pp3times/zmk-config-drift-v3-editor/PS3 Battery Pack Assembly/Drift-V3-Bottom-Pieces/Drift-V3-Bottom-Pieces.3mf

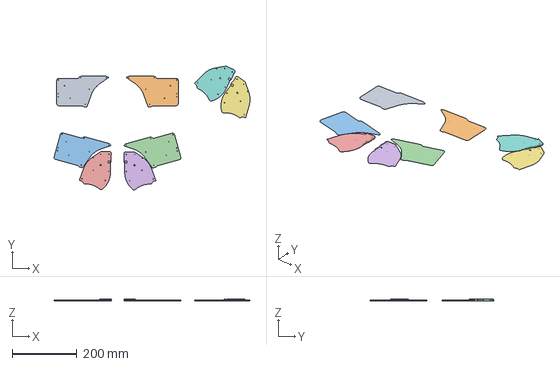
[picture p75: CAD file, 2025-06-20, last stored version]
PS3 Battery Pack Assembly/Drift-V3-Bottom-Pieces/Drift-V3-Bottom-Pieces.3mf
606.4 x 383.0 x 5.00 mm
Drift V3 bottom left.stl x 4
Drift V3 bottom right.stl x 4
