pp3times/zmk-config-drift-v3-editor/V3-MCU-Cover/MCU-Cover-left.stl

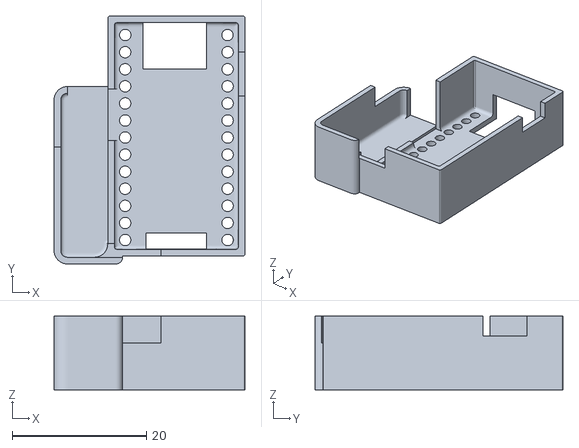
[picture p76: CAD file, 2025-06-20, last stored version]
V3-MCU-Cover/MCU-Cover-left.stl
28.4 x 36.9 x 11.0
