pp3times/zmk-config-drift-v3-editor/Outer-Acrylic/Bottom-Left-Acrylic.stl

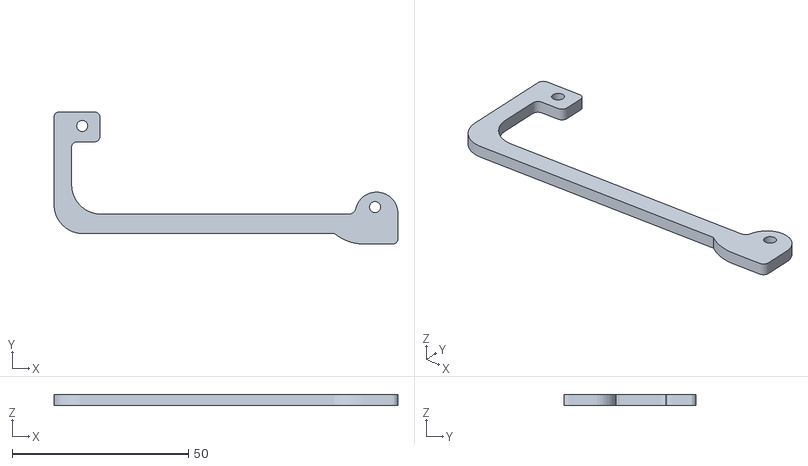
[picture p77: CAD file, 2025-06-21, last stored version]
Outer-Acrylic/Bottom-Left-Acrylic.stl
97.5 x 37.5 x 3.00
