pp3times/zmk-config-drift-v3-editor/printables/Cherry-MX/Otaru-Keycaps-by-Timception-Thumb-Key.stl

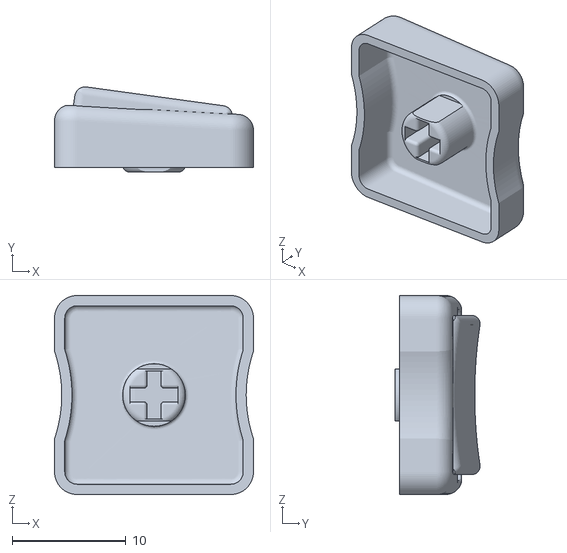
[picture p78: CAD file, 2025-06-18, last stored version]
printables/Cherry-MX/Otaru-Keycaps-by-Timception-Thumb-Key.stl
17.5 x 7.49 x 17.5
