pp3times/zmk-config-drift-v3-editor/printables/Low-Profile/Otaru-Keycaps-by-Timception-(Low-Profile)-Normal-Key.stl

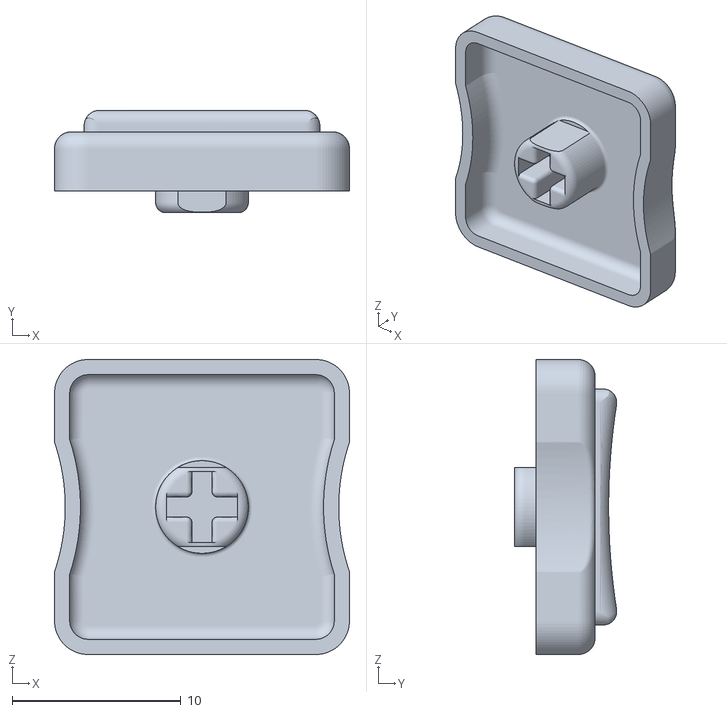
[picture p79: CAD file, 2025-06-18, last stored version]
printables/Low-Profile/Otaru-Keycaps-by-Timception-(Low-Profile)-Normal-Key.stl
17.5 x 6.08 x 17.5
