pp3times/zmk-config-drift-v3-editor/PS3 Battery Pack Assembly/Drift-V3-Battery-Expansion/Drift-V3-Battery-Expansion.3mf

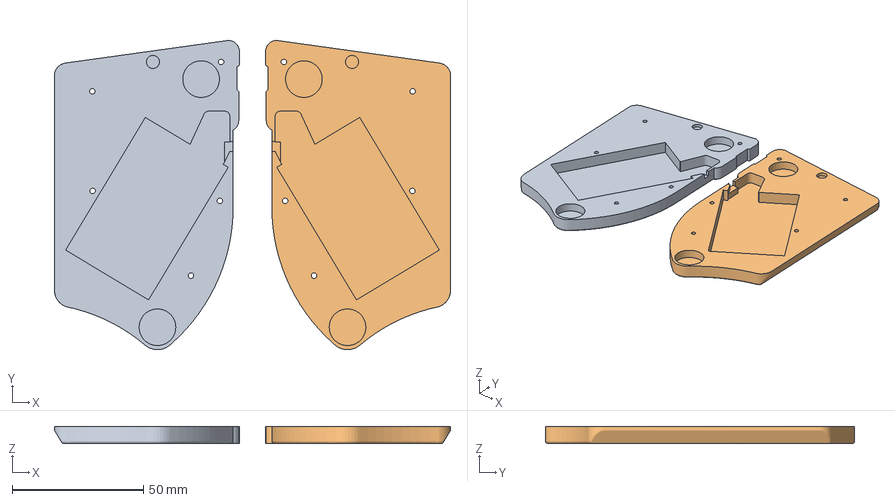
[picture p80: CAD file, 2025-06-20, last stored version]
PS3 Battery Pack Assembly/Drift-V3-Battery-Expansion/Drift-V3-Battery-Expansion.3mf
151.0 x 118.0 x 6.50 mm
Drift V3 Slim Battery Expansion.stl x 2
