pp3times/zmk-config-drift-v3-editor/Outer-Acrylic/Top-Acrylic.stl

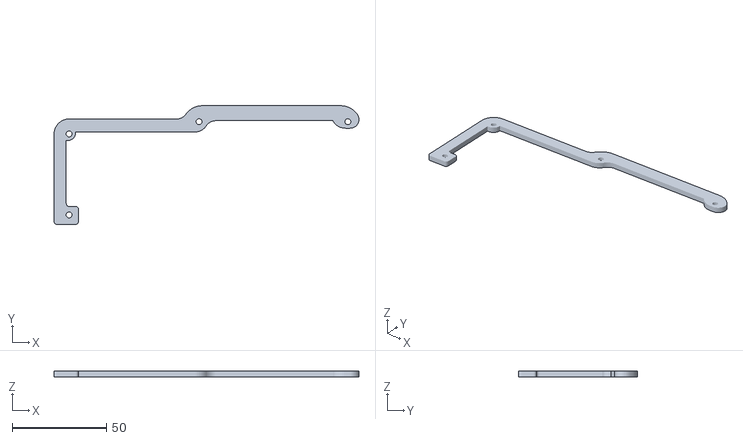
[picture p81: CAD file, 2025-06-21, last stored version]
Outer-Acrylic/Top-Acrylic.stl
161.9 x 63.0 x 3.00
