pp3times/zmk-config-drift-v3-editor/printables/Low-Profile/Otaru-Keycaps-by-Timception-(Low-Profile).3mf

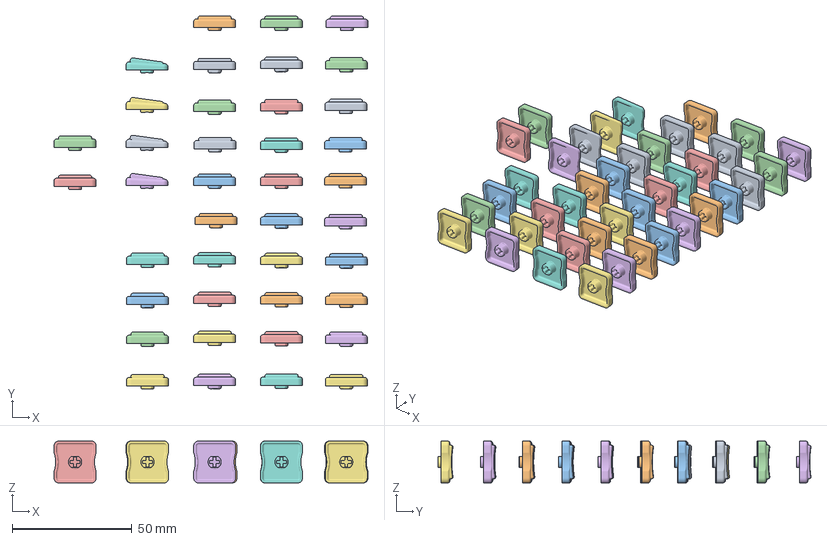
[picture p82: CAD file, 2025-06-18, last stored version]
printables/Low-Profile/Otaru-Keycaps-by-Timception-(Low-Profile).3mf
130.8 x 155.4 x 17.5 mm
Drift Keycaps by Timception Thumb Key LP.stl x 4
Drift Keycaps by Timception LP Thicker top (0.3).stl x 34
Drift Keycaps by Timception LP Thicker top (0.3) RIB.stl x 2
