pp3times/zmk-config-drift-v3-editor/PS3 Battery Pack Assembly/Drift-V3-Bottom-Pieces/Drift-V3-Bottom-Piece-1.stl

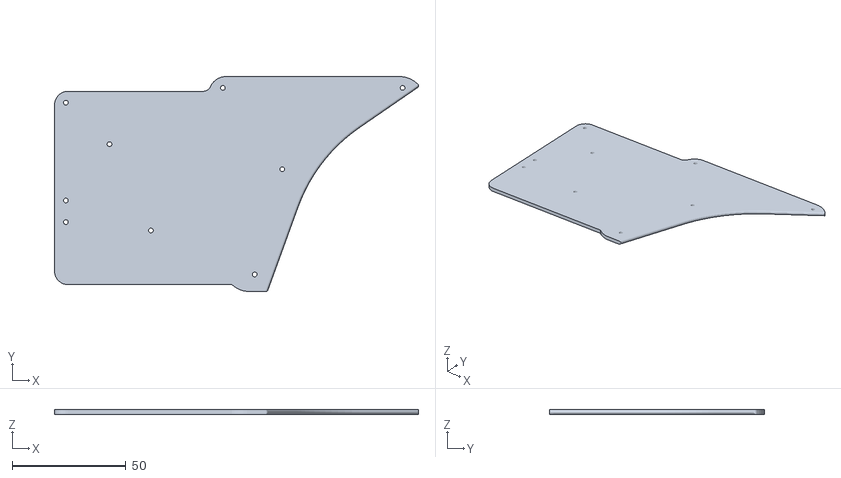
[picture p83: CAD file, 2025-06-20, last stored version]
PS3 Battery Pack Assembly/Drift-V3-Bottom-Pieces/Drift-V3-Bottom-Piece-1.stl
160.0 x 94.5 x 2.00
