pp3times/zmk-config-drift-v3-editor/Outer-Acrylic/Outer-Acrylic.3mf

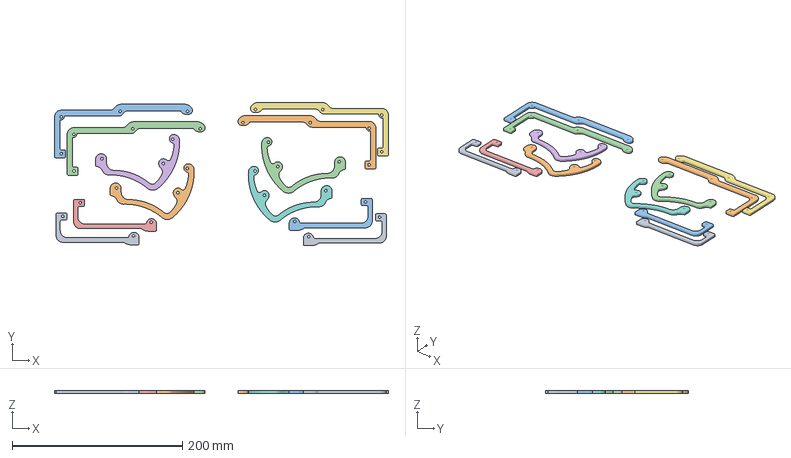
[picture p84: CAD file, 2025-06-21, last stored version]
Outer-Acrylic/Outer-Acrylic.3mf
391.9 x 168.2 x 3.00 mm
Bottom Left Acrylic x 4
Bottom Right Acrylic x 4
Top Acrylic x 4
